ZhangGaoxing/weather-station-arduino/Img/S3.jpg

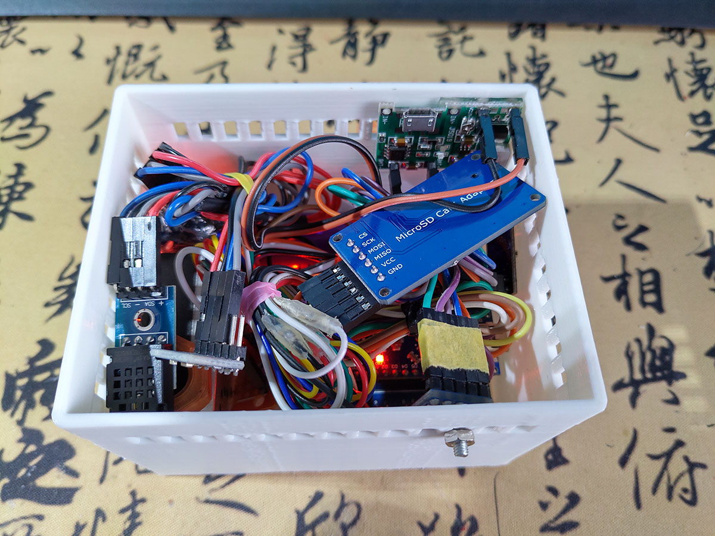
Img/S3.jpg
